phrickelberg/Proosha_IIIo/STL parts/Y-CORNERS/experimental/Y-CORNERS.dxf

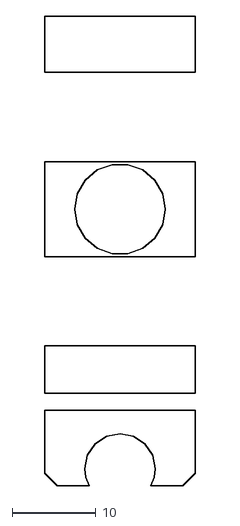
[picture p15: CAD file, 2014-09-25]
STL parts/Y-CORNERS/experimental/Y-CORNERS.dxf
18.0 x 56.0
