phrickelberg/Proosha_IIIo/STL parts/Y-CORNERS/Y-CORNERS-HOLLOW.stl

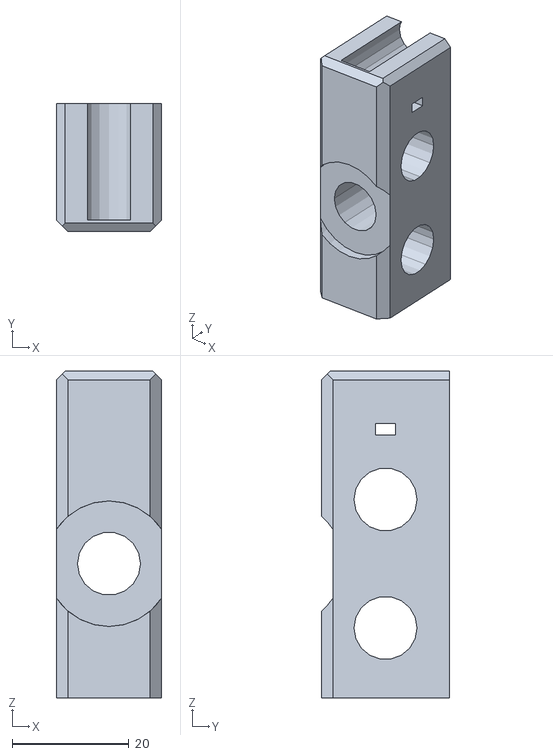
[picture p16: CAD file, 2014-10-24]
STL parts/Y-CORNERS/Y-CORNERS-HOLLOW.stl
18.0 x 22.0 x 56.0
