phrickelberg/Proosha_IIIo/STL parts/Y-IDLER/Y-IDLER.stl

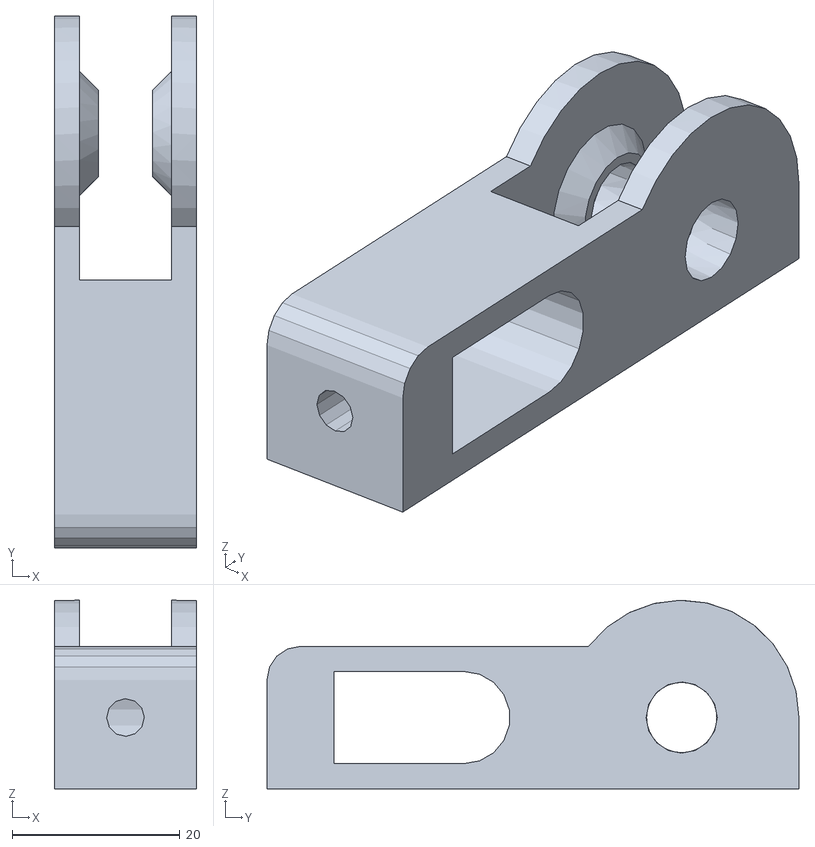
[picture p17: CAD file, 2014-02-21]
STL parts/Y-IDLER/Y-IDLER.stl
17.0 x 63.5 x 22.5
