phrickelberg/Proosha_IIIo/STL parts/Y-MOTOR/Y-MOTOR.stl

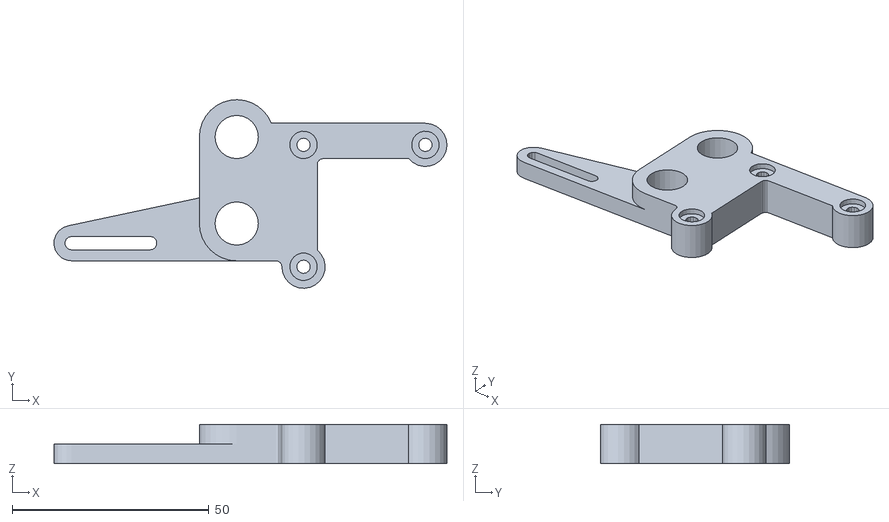
[picture p18: CAD file, 2014-02-21]
STL parts/Y-MOTOR/Y-MOTOR.stl
100.0 x 48.0 x 10.0
