phrickelberg/Proosha_IIIo/STL parts/Z-AXIS-BOTTOM/Z-AXIS-BOTTOM-RIGHT.stl

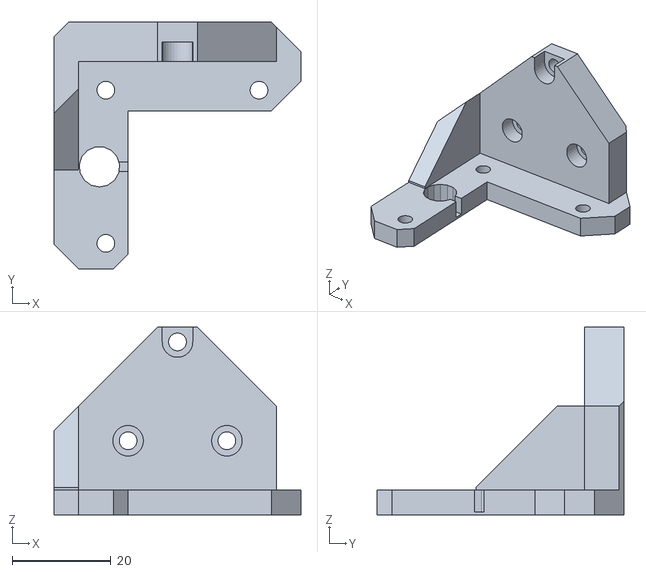
[picture p19: CAD file, 2014-02-21]
STL parts/Z-AXIS-BOTTOM/Z-AXIS-BOTTOM-RIGHT.stl
50.0 x 50.0 x 38.0
