phrickelberg/Proosha_IIIo/STL parts/Z-AXIS-TOP/Z-AXIS-TOP-LEFT-V2.stl

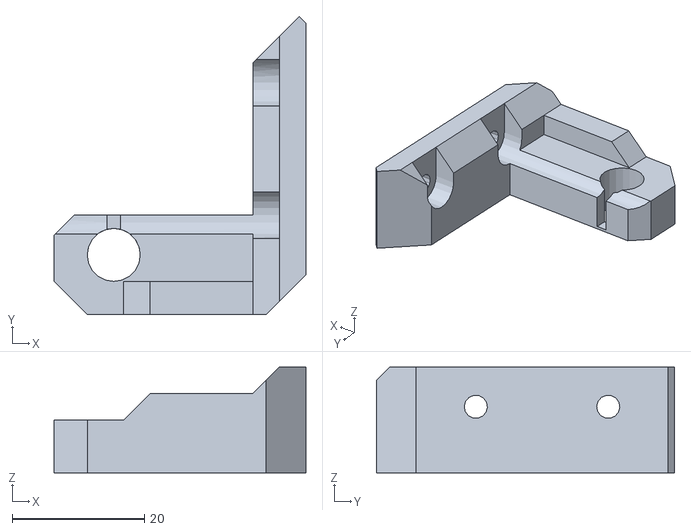
[picture p20: CAD file, 2014-02-21]
STL parts/Z-AXIS-TOP/Z-AXIS-TOP-LEFT-V2.stl
38.0 x 45.0 x 16.0
