phrickelberg/Proosha_IIIo/Frame/Proosha_IIIo-Frame-v1.dxf

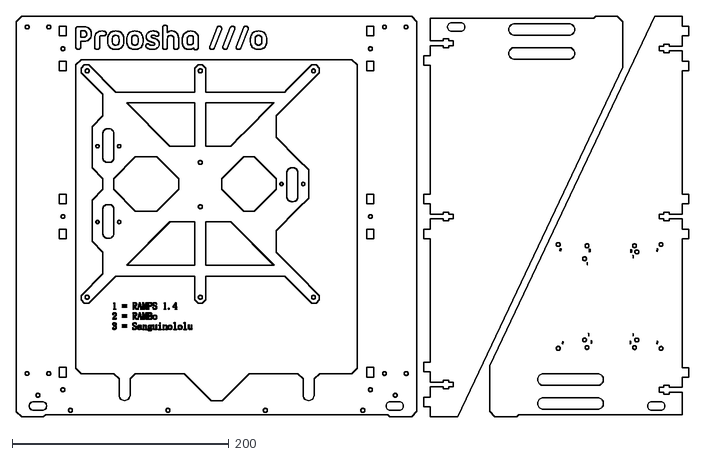
[picture p21: CAD file, 2014-02-22]
Frame/Proosha_IIIo-Frame-v1.dxf
620.9 x 370.1
