phrickelberg/Proosha_IIIo/STL parts/ENSTOP-Z-HOLDER/ENDSTOP-Z-HOLDER.stl

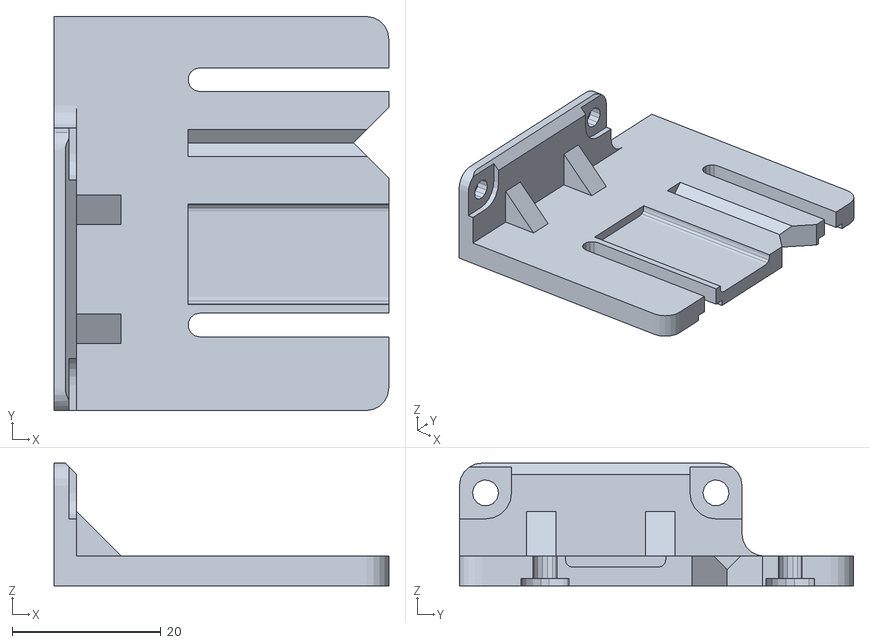
[picture p22: CAD file, 2014-02-21]
STL parts/ENSTOP-Z-HOLDER/ENDSTOP-Z-HOLDER.stl
45.0 x 53.0 x 16.5
