phrickelberg/Proosha_IIIo/STL parts/EXTRUDEUR/BODY-EXTRUDEUR-WADE-E3D-AB/e3d_extru_alnoa_1.75_ab-without-clip.stl

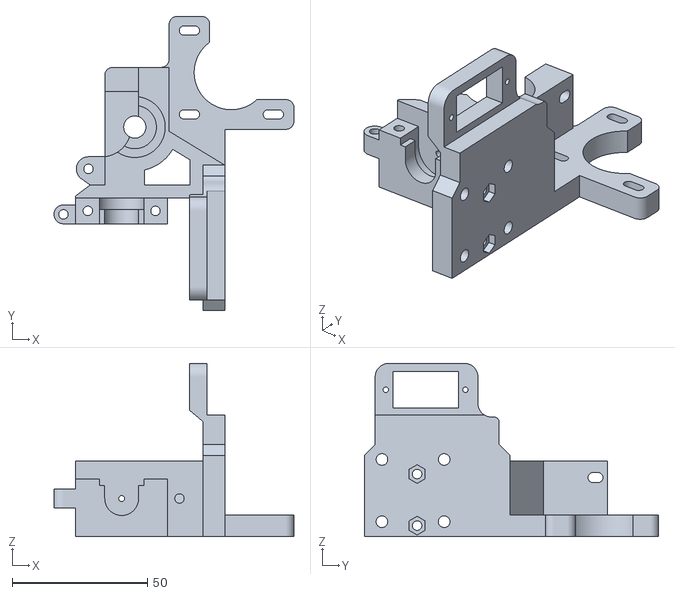
[picture p23: CAD file, 2014-09-25]
STL parts/EXTRUDEUR/BODY-EXTRUDEUR-WADE-E3D-AB/e3d_extru_alnoa_1.75_ab-without-clip.stl
88.7 x 108.7 x 64.0
