phrickelberg/Proosha_IIIo/STL parts/EXTRUDEUR/EXTRUDER-IDLER/EXTRUDER-IDLER.stl

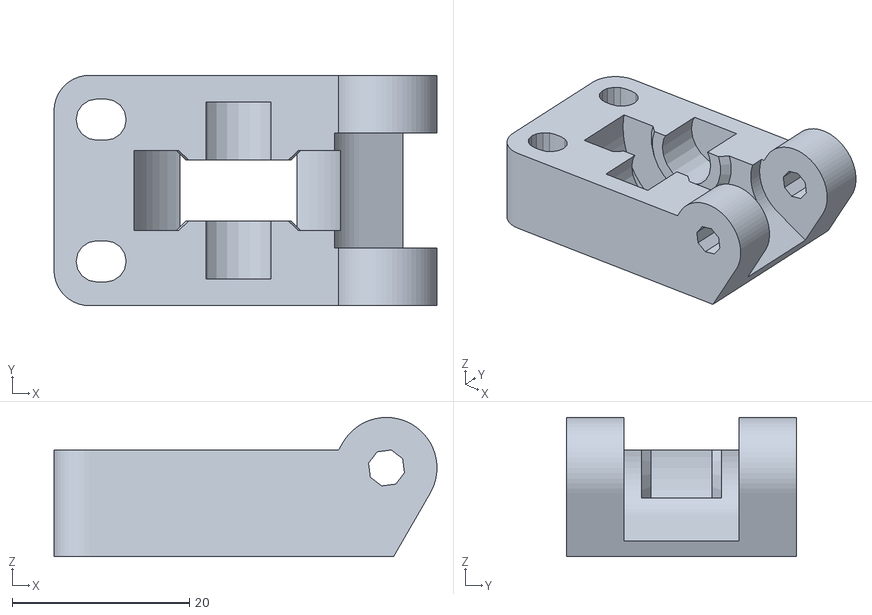
[picture p24: CAD file, 2014-02-21]
STL parts/EXTRUDEUR/EXTRUDER-IDLER/EXTRUDER-IDLER.stl
43.2 x 26.0 x 15.7
