phrickelberg/Proosha_IIIo/STL parts/Y-CORNERS/experimental/Y-CORNERS-4-ESTLCAM.dxf

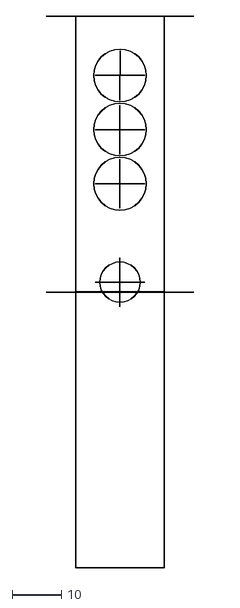
[picture p25: CAD file, 2014-09-25]
STL parts/Y-CORNERS/experimental/Y-CORNERS-4-ESTLCAM.dxf
30.0 x 112.0
