phrickelberg/Proosha_IIIo/STL parts/X-END-IDLER/X-END-IDLER.stl

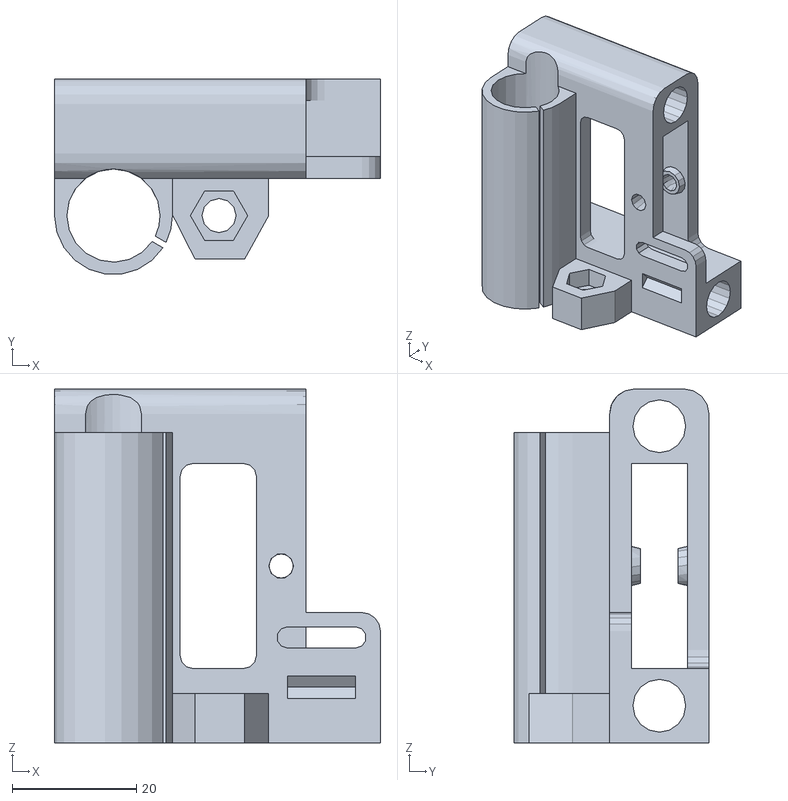
[picture p26: CAD file, 2014-02-21]
STL parts/X-END-IDLER/X-END-IDLER.stl
52.5 x 31.4 x 57.0
