phrickelberg/Proosha_IIIo/STL parts/Y-CORNERS/Y-CORNERS.stl

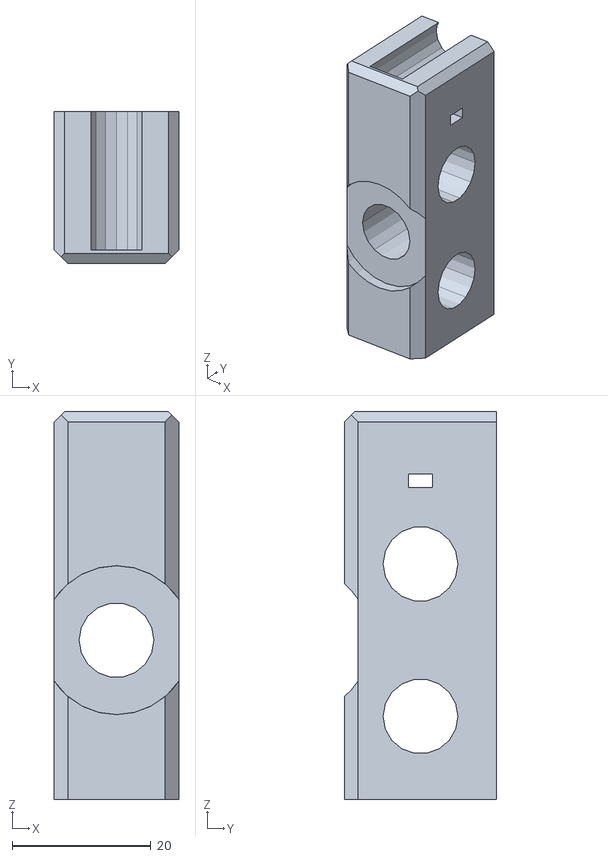
[picture p27: CAD file, 2014-02-21]
STL parts/Y-CORNERS/Y-CORNERS.stl
18.0 x 22.0 x 56.0
